Settis/6502/prog/SDcard/pulseView/goodRatio.png

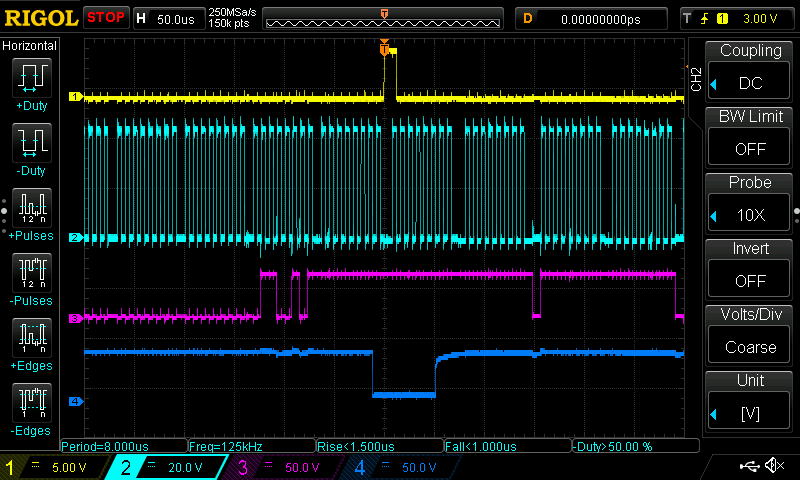
prog/SDcard/pulseView/goodRatio.png
