Settis/6502/prog/SDcard/pulseView/goodRatioZoom1.png

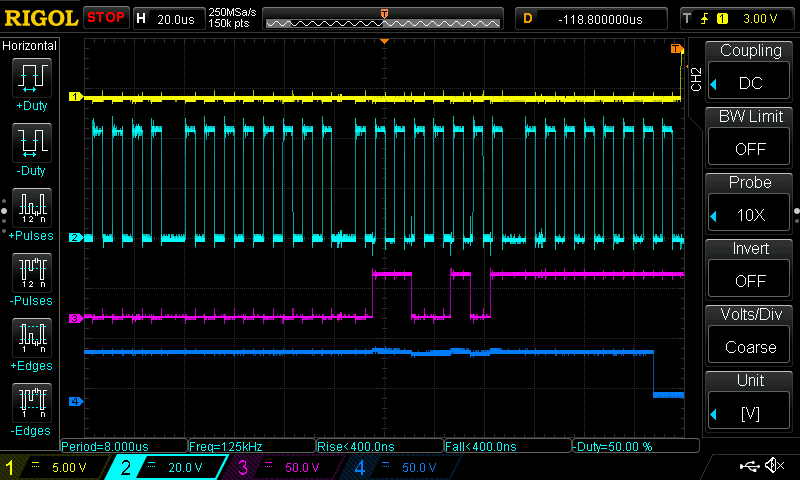
prog/SDcard/pulseView/goodRatioZoom1.png
