Settis/6502/prog/SDcard/pulseView/goodRatioZoom2.png

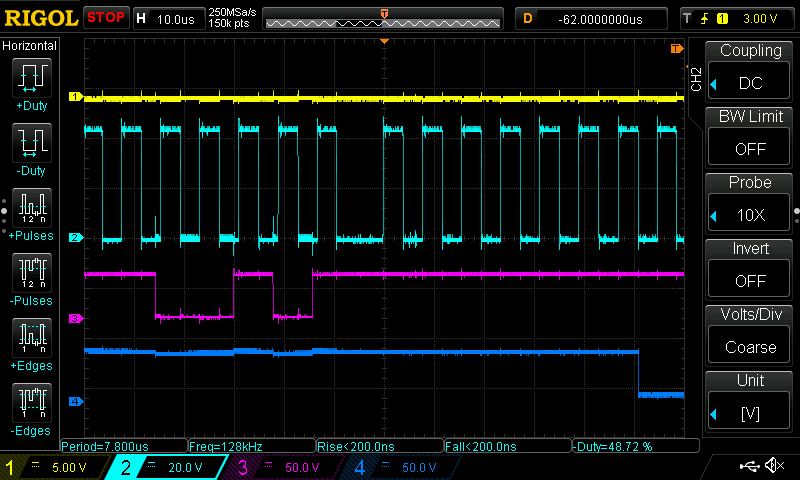
prog/SDcard/pulseView/goodRatioZoom2.png
