Settis/6502/prog/SDcard/pulseView/initial.png

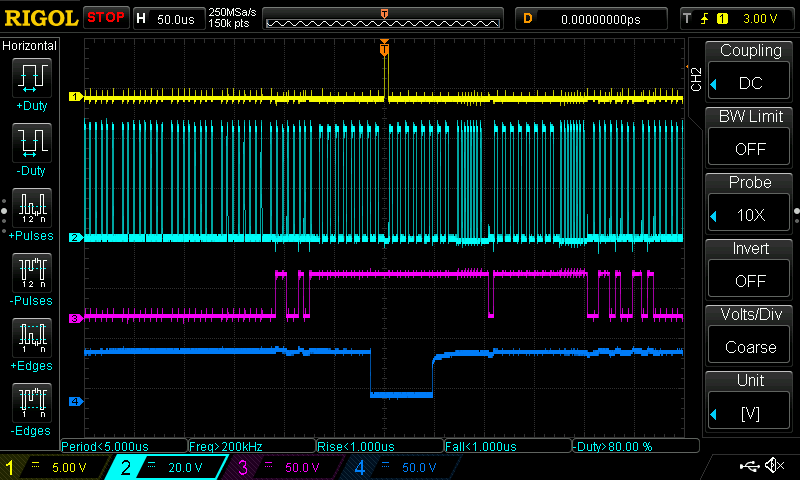
prog/SDcard/pulseView/initial.png
