Settis/6502/prog/SDcard/pulseView/initialZoom1.png

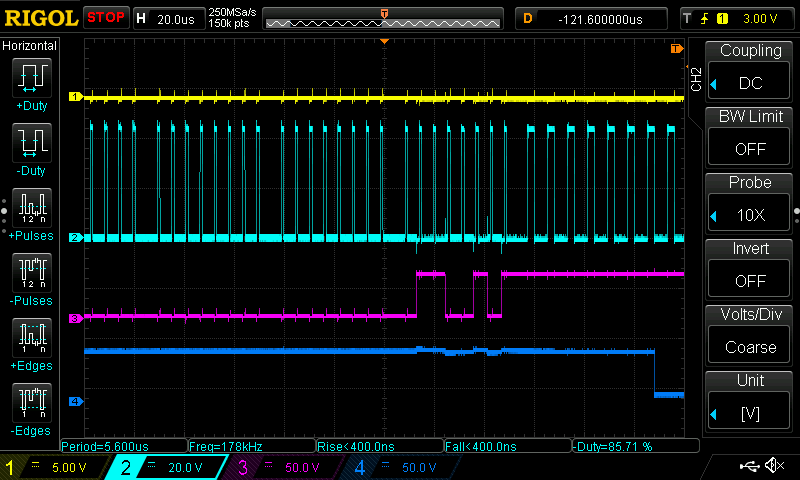
prog/SDcard/pulseView/initialZoom1.png
