Settis/6502/prog/SDcard/pulseView/initialZoom2.png

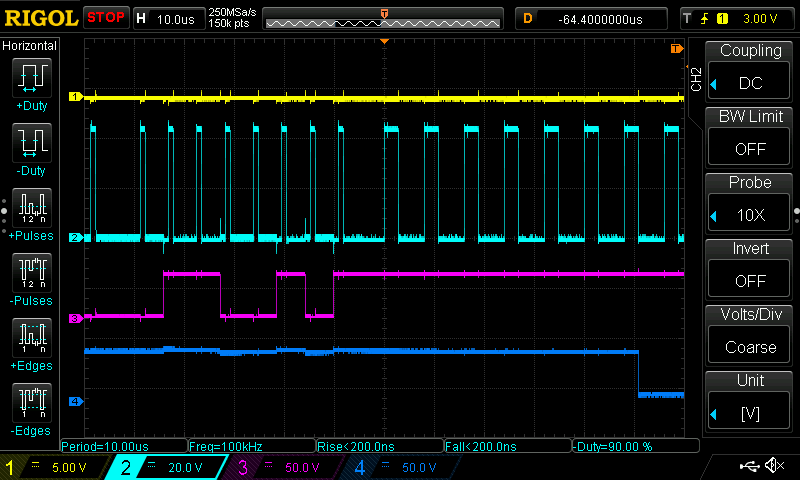
prog/SDcard/pulseView/initialZoom2.png
