Settis/6502/schematics/VGA_TO_VIA/VGA_TO_VIA.kicad_pcb

## KiCad design hardware/kicad/atmosmesh-bench/atmosmesh-bench.kicad_pcb

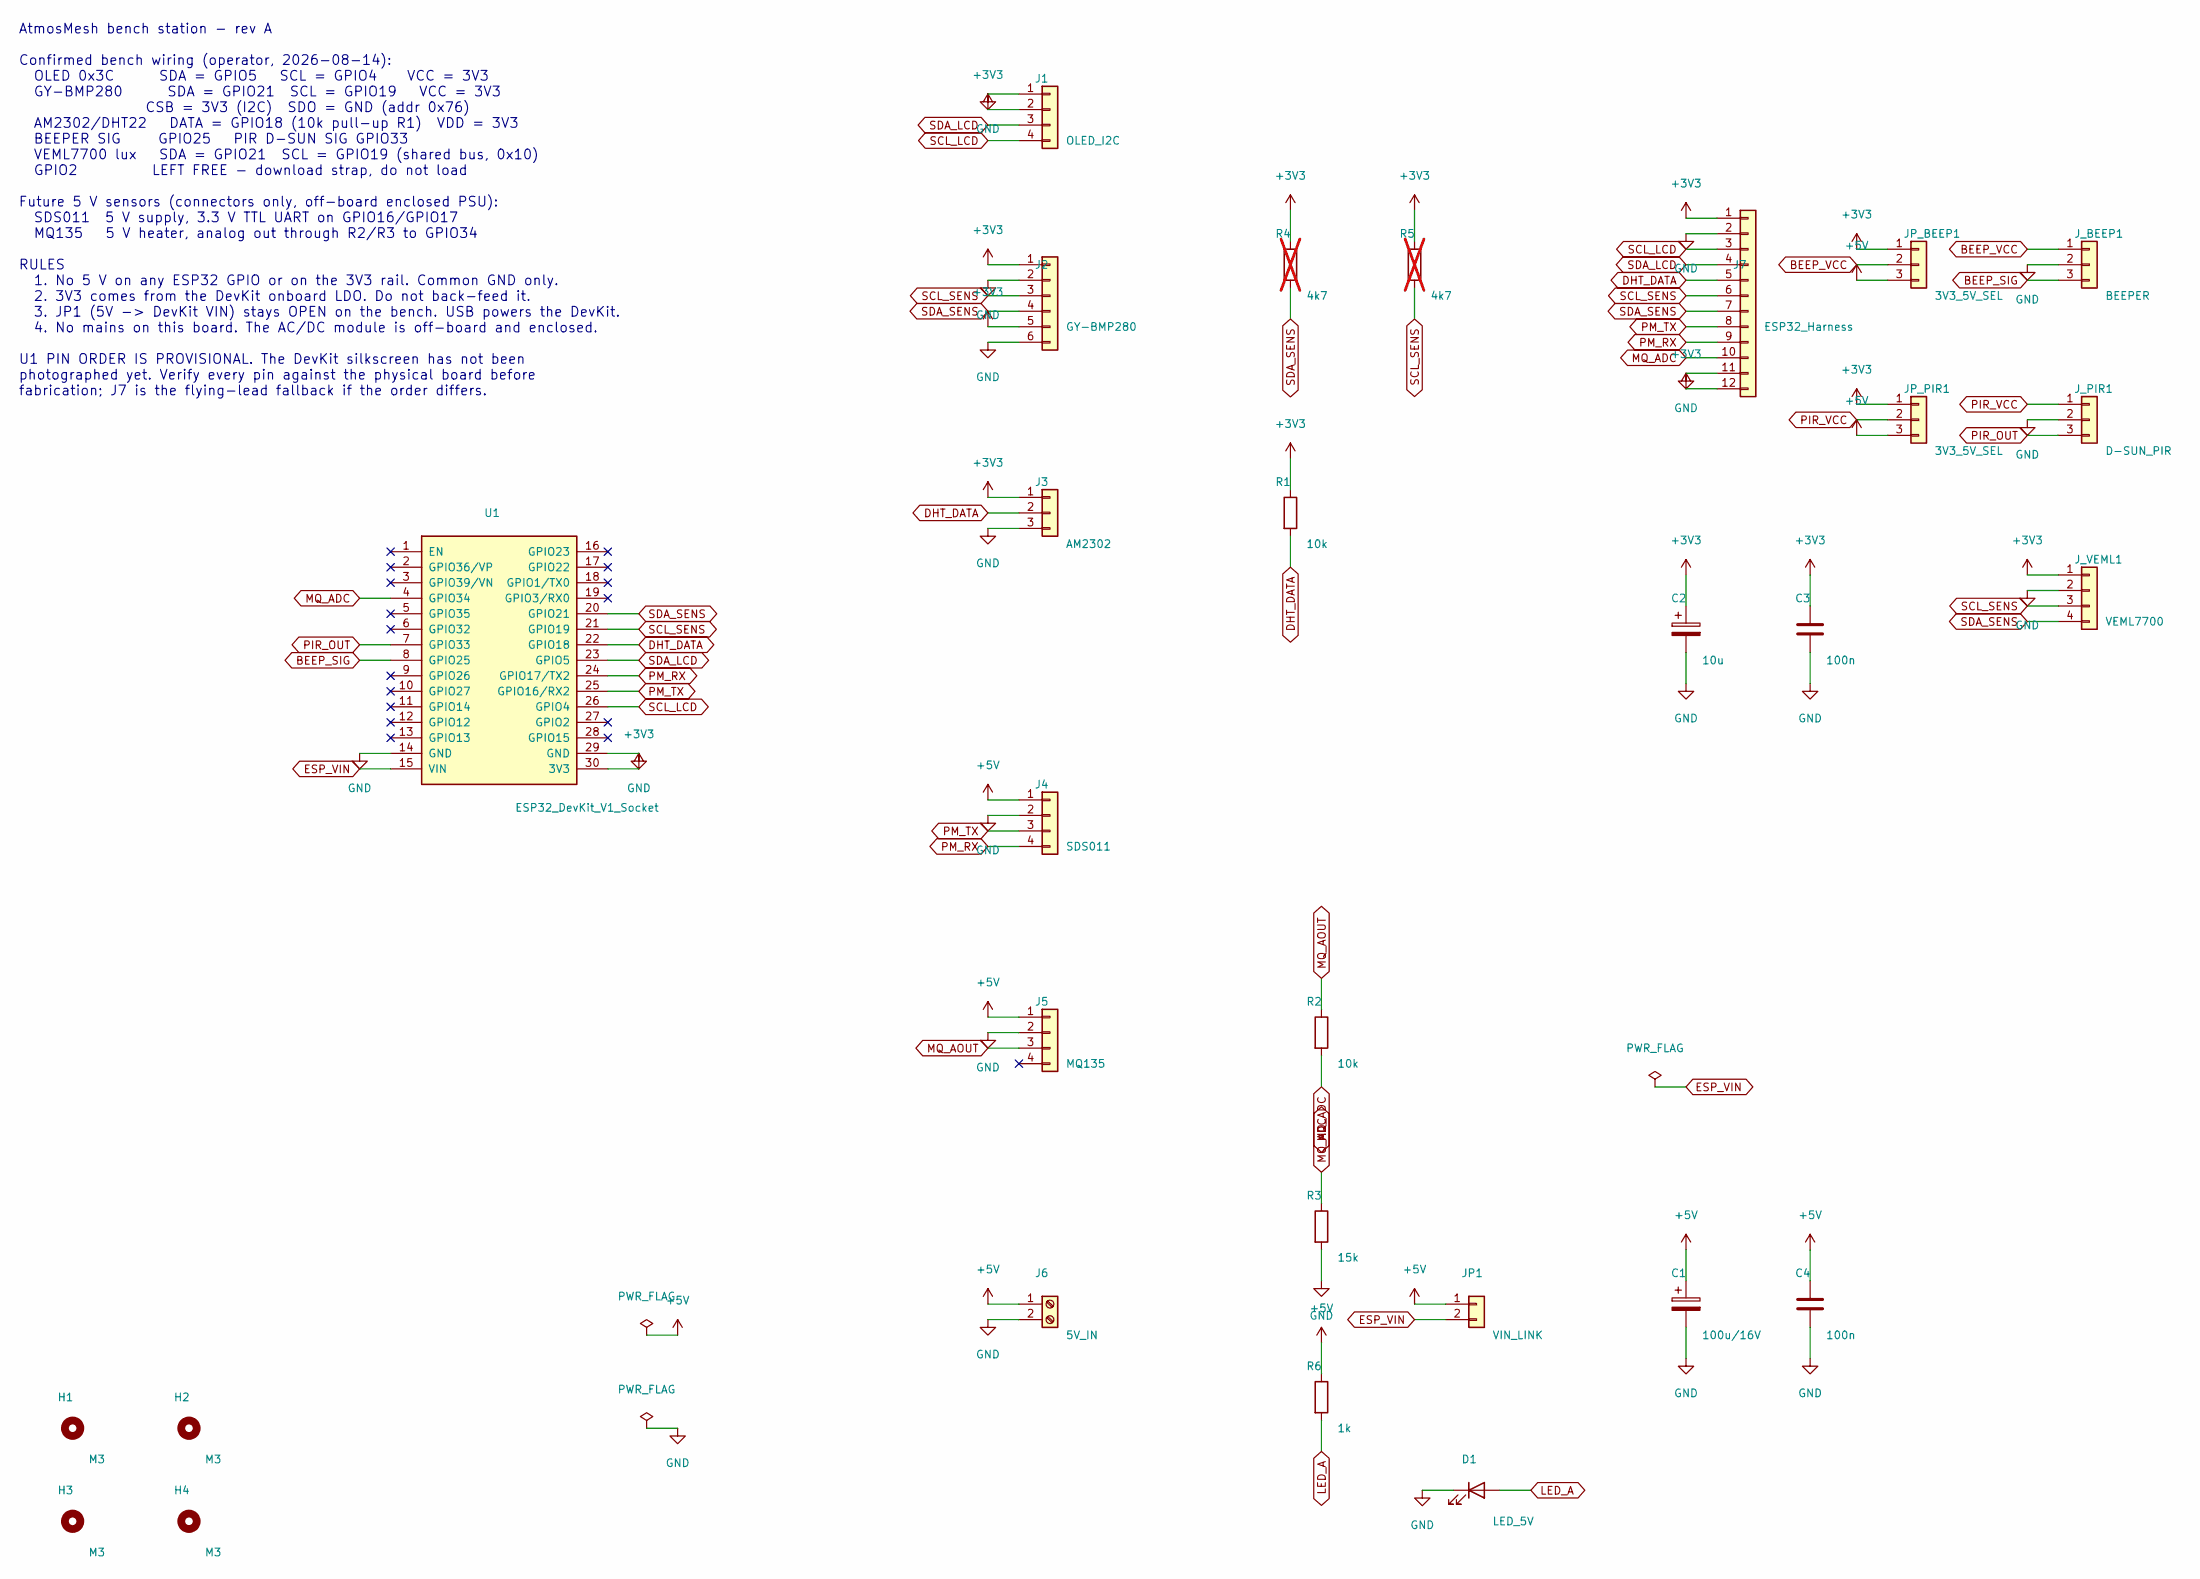
[picture p30: schematic atmosmesh-bench.kicad_sch, AtmosMesh bench station]

Parts:
C1: 100u/16V; CP_Radial_D6.3mm_P2.50mm
C2: 10u; CP_Radial_D5.0mm_P2.00mm
C3, C4: 100n; C_Disc_D5.0mm_W2.5mm_P5.00mm
D1: LED_5V; LED_D3.0mm
H1, H2, H3, H4: M3; MountingHole_3.2mm_M3
J1: OLED_I2C; PinHeader_1x04_P2.54mm_Vertical
J2: GY-BMP280; PinHeader_1x06_P2.54mm_Vertical
J3: AM2302; PinHeader_1x03_P2.54mm_Vertical
J4: SDS011; PinHeader_1x04_P2.54mm_Vertical
J5: MQ135; PinHeader_1x04_P2.54mm_Vertical
J6: 5V_IN; TerminalBlock_Phoenix_MKDS-1,5-2-5.08_1x02_P5.08mm_Horizont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
J7: ESP32_Harness; PinHeader_1x12_P2.54mm_Vertical
JP1: VIN_LINK; PinHeader_1x02_P2.54mm_Vertical
JP_BEEP1: 3V3_5V_SEL; PinHeader_1x03_P2.54mm_Vertical
JP_PIR1: 3V3_5V_SEL; PinHeader_1x03_P2.54mm_Vertical
J_BEEP1: BEEPER; PinHeader_1x03_P2.54mm_Vertical
J_PIR1: D-SUN_PIR; PinHeader_1x03_P2.54mm_Vertical
J_VEML1: VEML7700; PinHeader_1x04_P2.54mm_Vertical
R1, R2: 10k; R_Axial_DIN0207_L6.3mm_D2.5mm_P7.62mm_Horizontal
R3: 15k; R_Axial_DIN0207_L6.3mm_D2.5mm_P7.62mm_Horizontal
R4, R5: 4k7; R_Axial_DIN0207_L6.3mm_D2.5mm_P7.62mm_Horizontal; not fitted
R6: 1k; R_Axial_DIN0207_L6.3mm_D2.5mm_P7.62mm_Horizontal
U1: ESP32_DevKit_V1_Socket; ESP32_DevKit_1x15x2_P25.40mm

Connections:
+3V3: C2.1, C3.1, J1.2, J2.1, J2.5, J3.1, J7.1, J7.12, JP_BEEP1.1, JP_PIR1.1, J_VEML1.1, R1.1, R4.1, R5.1, U1.30 (3V3)
+5V: C1.1, C4.1, J4.1, J5.1, J6.1, JP1.1, JP_BEEP1.3, JP_PIR1.3, R6.1
BEEP_SIG: J_BEEP1.3, U1.8 (GPIO25)
BEEP_VCC: JP_BEEP1.2, J_BEEP1.1
DHT_DATA: J3.2, J7.5, R1.2, U1.22 (GPIO18)
ESP_VIN: JP1.2, U1.15 (VIN)
GND: C1.2, C2.2, C3.2, C4.2, D1.1 (K), J1.1, J2.2, J2.6, J3.3, J4.2, J5.2, J6.2, J7.2, J7.11, J_BEEP1.2, J_PIR1.2, J_VEML1.2, R3.2, U1.14 (GND), U1.29 (GND)
LED_A: D1.2 (A), R6.2
MQ_ADC: J7.10, R2.2, R3.1, U1.4 (GPIO34)
MQ_AOUT: J5.3, R2.1
PIR_OUT: J_PIR1.3, U1.7 (GPIO33)
PIR_VCC: JP_PIR1.2, J_PIR1.1
PM_RX: J4.4, J7.9, U1.24 (GPIO17/TX2)
PM_TX: J4.3, J7.8, U1.25 (GPIO16/RX2)
SCL_LCD: J1.4, J7.3, U1.26 (GPIO4)
SCL_SENS: J2.3, J7.6, J_VEML1.3, R5.2, U1.21 (GPIO19)
SDA_LCD: J1.3, J7.4, U1.23 (GPIO5)
SDA_SENS: J2.4, J7.7, J_VEML1.4, R4.2, U1.20 (GPIO21)

Notes on the sheet:
AtmosMesh bench station - rev A Confirmed bench wiring (operator, 2026-08-14): OLED 0x3C SDA = GPIO5 SCL = GPIO4 VCC = 3V3 GY-BMP280 SDA = GPIO21 SCL = GPIO19 VCC = 3V3 CSB = 3V3 (I2C) SDO = GND (addr 0x76) AM2302/DHT22 DATA = GPIO18 (10k pull-up R1) VDD = 3V3 BEEPER SIG GPIO25 PIR D-SUN SIG GPIO33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

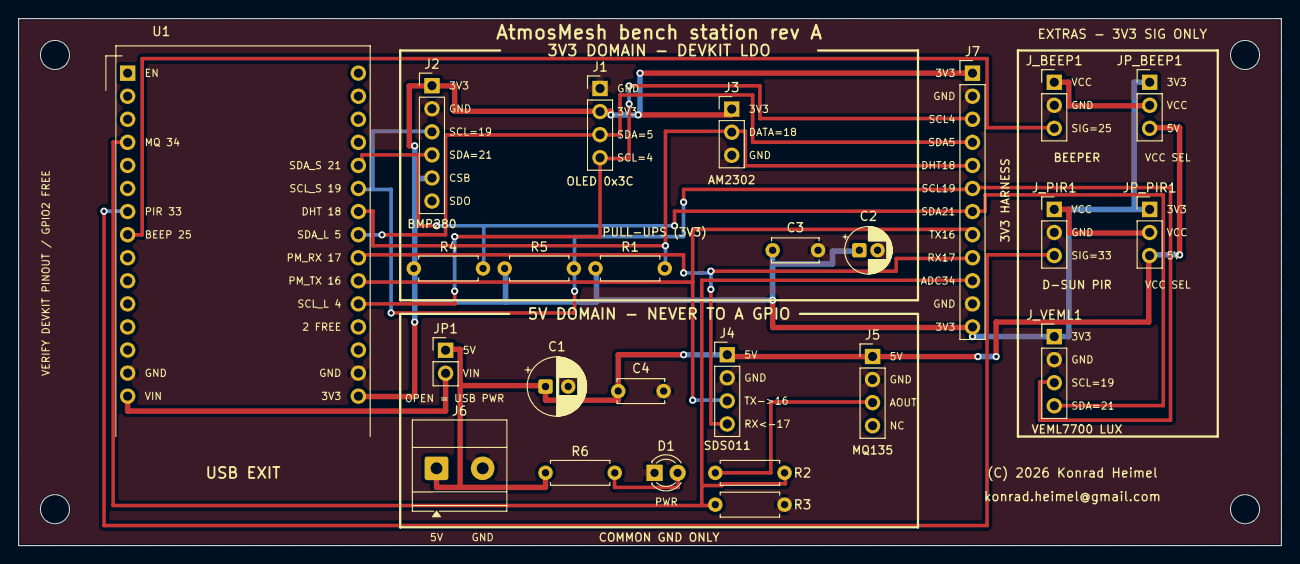
[picture p31: board atmosmesh-bench.kicad_pcb from above]

Board: 2 copper layers, 139.0 x 58.0 mm, 29 parts (0 on the bottom side), 18 nets.
