Settis/6502/logisim/progs/images.asm

satellite_data:
	dc $3d
	dc $66
	dc $4c
	dc $24
	dc $1b
	dc $1a
	dc $19
	dc $18
	dc $17
	dc $16
	dc $15
	dc $14
	dc $13
	dc $3c
	dc $3b
	dc $3a
	dc $34
	dc $33
	dc $32
	dc $5d
	dc $5c
	dc $52
	dc $51
	dc $50
	dc $4f
	dc $7e
	dc $7d
	dc $72
	dc $71
	dc $70
	dc $6f
	dc $6e
	dc $9f
	dc $9e
	dc $93
	dc $92
	dc $90
	dc $8f
	dc $8e
	dc $8d
	dc $bf
	dc $be
	dc $b4
	dc $b3
	dc $b0
	dc $af
	dc $ae
	dc $ad
	dc $ac
	dc $df
	dc $d5
	dc $d4
	dc $cf
	dc $ce
	dc $cd
	dc $cc
	dc $cb
	dc $ff
	dc $f6
	dc $f5
	dc $ef
	dc $ed
	dc $ec
	dc $eb
	dc $ea
	dc $1f
	dc $17
	dc $16
	dc $0f
	dc $0c
	dc $0b
	dc $0a
	dc $09
	dc $3f
	dc $38
	dc $37
	dc $36
	dc $35
	dc $30
	dc $2f
	dc $2b
	dc $2a
	dc $29
	dc $28
	dc $5f
	dc $59
	dc $58
	dc $56
	dc $55
	dc $54
	dc $51
	dc $50
	dc $4f
	dc $4a
	dc $49
	dc $48
	dc $47
	dc $7f
	dc $7e
	dc $7a
	dc $79
	dc $75
	dc $74
	dc $73
	dc $72
	dc $71
	dc $70
	dc $6f
	dc $69
	dc $68
	dc $67
	dc $66
	dc $9f
	dc $9e
	dc $9b
	dc $9a
	dc $94
	dc $93
	dc $92
	dc $91
	dc $90
	dc $8f
	dc $88
	dc $87
	dc $86
	dc $85
	dc $be
	dc $bd
	dc $bc
	dc $bb
	dc $b4
	dc $b3
	dc $b2
	dc $b1
	dc $b0
	dc $a7
	dc $a6
	dc $a5
	dc $a4
	dc $dd
	dc $dc
	dc $d5
	dc $d4
	dc $d3
	dc $d2
	dc $d1
	dc $d0
	dc $c6
	dc $c5
	dc $c4
	dc $c3
	dc $fd
	dc $fc
	dc $fb
	dc $fa
	dc $f6
	dc $f5
	dc $f4
	dc $f3
	dc $f2
	dc $f1
	dc $f0
	dc $ef
	dc $e5
	dc $e4
	dc $e3
	dc $e2
	dc $1d
	dc $1c
	dc $1b
	dc $1a
	dc $19
	dc $18
	dc $17
	dc $16
	dc $15
	dc $14
	dc $13
	dc $10
	dc $0f
	dc $0e
	dc $04
	dc $03
	dc $02
	dc $01
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
	dc.w artichoke_data
	dc.w dill_data
	dc.w blueberries_data
	dc.w satellite2_data
	dc.w satellite3_data
	dc.w cherry_data
	dc.w atoms_data
	dc.w chiliPepper_data
	dc.w onion_data
	dc.w rocket_data
	dc.w microchip_data
	dc.w robot_data
	dc.w robot2_data
	dc.w garlic_data
	dc.w floppy_data
	dc.w broccoli_data
