Settis/6502/prog/std/initSegments.asm

    IFNCONST ZP_VARS_START
ZP_VARS_START = $0
    ENDIF
    
    SEG.U zpVars
    ORG ZP_VARS_START

    IFNCONST CODE_START
CODE_START = $200
    ENDIF

    SEG code
    ORG CODE_START

    IFNCONST UPPER_RAM_START
UPPER_RAM_START = $7FFF
    ENDIF

    SEG.U upperRam
    ORG UPPER_RAM_START
