Settis/6502/prog/std/io_errors.asm

IO_OK = $0
IO_END_OF_FILE = $1
IO_FILE_NOT_FOUND = $2
IO_INVALID_FILENAME_FORMAT = $3
IO_SD_BUSY_BEFORE_GO_IDLE_STATE = $4
IO_SD_BUSY_AFTER_GO_IDLE_STATE = $5
IO_SD_NOT_IDLE_AFTER_GO_IDLE_STATE = $6
IO_SD_BUSY_BEFORE_SEND_IF_COND = $7
IO_SD_BUSY_AFTER_SEND_IF_COND = $8
IO_SD_NOT_IDLE_AFTER_SEND_IF_COND = $9
IO_SD_BUSY_BEFORE_APP_CMD = $A
IO_SD_BUSY_AFTER_APP_CMD = $B
IO_SD_BUSY_BEFORE_APP_SEND_OP_COND = $C
IO_SD_BUSY_AFTER_APP_SEND_OP_COND = $D
IO_SD_ERROR_AFTER_APP_SEND_OP_COND = $E
IO_SD_BUSY_BEFORE_READ_SECTOR = $F
IO_SD_BUSY_AFTER_READ_SECTOR = $10
IO_SD_ERROR_AFTER_READ_SECTOR = $11
IO_SD_DATA_TOKEN_DID_NOT_RECEIVED_AFTER_READ_SECTOR = $12
IO_WRONG_BOOT_SIGNATURE = $13
IO_WRONG_PARTITION_TYPE = $14
IO_WRONG_BYTES_PER_LOGICAL_SECTOR = $15
IO_WRONG_FATS_NUMBER = $16
IO_WRONG_FAT_MEDIA_DESCRIPTOR = $17
IO_ZERO_SECTORS_PER_CLUSTER = $18
IO_FAT_END_OF_CLUSTERS = $19
