Settis/6502/logisim/tools/microcodeSpec.yaml

address:
  - type: counter
    size: 4
  - type: instruction
    size: 8
  - type: condition
    name: CF
  - type: condition
    name: ZF
  - type: condition
    name: VF
  - type: condition
    name: NF
outBits:
  - name: AddrSelecter
    type: enum
    offset: 0
    values:
      - PC
      - Addr
      - ZP
      - SP
  - name: CntLIn
    offset: 2
  - name: CntHIn
    offset: 3
  - name: CntEn
    offset: 4
  - name: InstIn
    offset: 5
  - name: AluM
    offset: 6
  - name: SecondSelect
    type: enum
    offset: 7
    values:
      - Alu0
      - AluA
      - AluX
      - AluY
      - AluSp
      - AluAddrL
      - AluAddrH
      - AluB
  - name: OpSelect
    type: enum
    offset: 10
    values:
      - Add
      - Sub
      - Or
      - And
      - Xor
      - ASL
      - LSR
      - RTL
      - RTR
      - AddAddrLAndY
  - name: AluOutSelect
    type: enum
    offset: 14
    values:
      - AluToB
      - AluToA
      - AluToX
      - AluToY
      - AluToSp
      - AluToAddrH
      - AluToAddrL
      - AluToF
  - name: DataOutSelect
    type: enum
    offset: 17
    values:
      - DataOutNull
      - DataOutA
      - DataOutB
      - DataOutPcH
      - DataOutPcL
      - DataOutX
      - DataOutY
      - DataOutF
  - name: FlagInst
    type: enum
    offset: 20
    values:
      - FlagNone
      - ClearCarry
      - SetCarry
      - ClearInt
      - SetInt
      - ClearOverfl
      - ClearDec
      - SetDec
  - name: UseCF
    type: enum
    offset: 23
    values:
      - CF0
      - CF1
      - LCF
      - CF
  - name: CFEn
    offset: 25
  - name: ZFEn
    offset: 26
  - name: VFEn
    offset: 27
  - name: NFEn
    offset: 28
  - name: AddrShift
    offset: 29
  - name: MicRst
    offset: 30
defaultStartSteps:
  - InstIn | CntEn
defaultEndSteps:
  - MicRst
prefixSteps:
  - name: ZP
    steps:
      - AluToAddrH
      - AluM | AluToAddrL | CntEn
  - name: ZPX
    steps:
      - AluToAddrH
      - AluM | AluX | Add | AluToAddrL | CntEn
  - name: ZPY
    steps:
      - AluToAddrH
      - AluM | AluY | Add | AluToAddrL | CntEn
  - name: Abs
    steps:
      - AluM | AluToAddrL | CntEn
      - AluM | AluToAddrH | CntEn
  - name: AbsX
    steps:
      - AluM | AluX | Add | AluToAddrL | CntEn
      - AluM | LCF | Add | AluToAddrH | CntEn
  - name: AbsY
    steps:
      - AluM | AluY | Add | AluToAddrL | CntEn
      - AluM | LCF | Add | AluToAddrH | CntEn
  - name: IndX
    steps:
      - AluToAddrH
      - AluM | AluX | Add | AluToAddrL | CntEn
      - Addr | AluM | AluToB
      - AluAddrL | CF1 | Add | AluToAddrL
      - Addr | AluM | AluToAddrH
      - AluB | AluToAddrL
  - name: IndY
    steps:
      - AluToAddrH
      - AluM | AluToAddrL | CntEn
      - Addr | AluM | AluToB
      - AluAddrL | CF1 | Add | AluToAddrL
      - Addr | AluM | AluToAddrH
      - AluB | AluToAddrL
      - AddAddrLAndY | AluToAddrL
      - AluAddrH | LCF | Add | AluToAddrH
  - name: BrPos
    steps:
      - AluM | AluToB | CntEn
      - AluB | AddrShift | CntLIn | CntHIn
  - name: BrNeg
    steps:
      - CntEn
commands:
  - name: "ADC #$44"
    value: 0x69
    steps:
      - AluM | AluA | Add | CF | AluToA | CntEn | NFEn | VFEn | ZFEn | CFEn
  - name: "ADC $44"
    value: 0x65
    prefix: ZP
    steps:
      - Addr | AluM | AluA | Add | CF | AluToA | NFEn | VFEn | ZFEn | CFEn
  - name: "ADC $44,X"
    value: 0x75
    prefix: ZPX
    steps:
      - Addr | AluM | AluA | Add | CF | AluToA | NFEn | VFEn | ZFEn | CFEn
  - name: "ADC $4400"
    value: 0x6d
    prefix: Abs
    steps:
      - Addr | AluM | AluA | Add | CF | AluToA | NFEn | VFEn | ZFEn | CFEn
  - name: "ADC $4400,X"
    value: 0x7d
    prefix: AbsX
    steps:
      - Addr | AluM | AluA | Add | CF | AluToA | NFEn | VFEn | ZFEn | CFEn
  - name: "ADC $4400,Y"
    value: 0x79
    prefix: AbsY
    steps:
      - Addr | AluM | AluA | Add | CF | AluToA | NFEn | VFEn | ZFEn | CFEn
  - name: "ADC ($44,X)"
    value: 0x61
    prefix: IndX
    steps:
      - Addr | AluM | AluA | Add | CF | AluToA | NFEn | VFEn | ZFEn | CFEn
  - name: "ADC ($44),Y"
    value: 0x71
    prefix: IndY
    steps:
      - Addr | AluM | AluA | Add | CF | AluToA | NFEn | VFEn | ZFEn | CFEn
  - name: "AND #$44"
    value: 0x29
    steps:
      - AluM | AluA | And | AluToA | NFEn | ZFEn | CntEn
  - name: "AND $44"
    value: 0x25
    prefix: ZP
    steps:
      - Addr | AluM | AluA | And | AluToA | NFEn | ZFEn
  - name: "AND $44,X"
    value: 0x35
    prefix: ZPX
    steps:
      - Addr | AluM | AluA | And | AluToA | NFEn | ZFEn
  - name: "AND $4400"
    value: 0x2d
    prefix: Abs
    steps:
      - Addr | AluM | AluA | And | AluToA | NFEn | ZFEn
  - name: "AND $4400,X"
    value: 0x3d
    prefix: AbsX
    steps:
      - Addr | AluM | AluA | And | AluToA | NFEn | ZFEn
  - name: "AND $4400,Y"
    value: 0x39
    prefix: AbsY
    steps:
      - Addr | AluM | AluA | And | AluToA | NFEn | ZFEn
  - name: "AND ($44,X)"
    value: 0x21
    prefix: IndX
    steps:
      - Addr | AluM | AluA | And | AluToA | NFEn | ZFEn
  - name: "AND ($44),Y"
    value: 0x31
    prefix: IndY
    steps:
      - Addr | AluM | AluA | And | AluToA | NFEn | ZFEn
  - name: "ASL A"
    value: 0x0a
    steps:
      - ASL | AluToA | NFEn | ZFEn | CFEn
  - name: "ASL $44"
    value: 0x06
    prefix: ZP
    steps:
      - Addr | AluM | ASL | AluToB | NFEn | ZFEn | CFEn
      - Addr | DataOutB
  - name: "ASL $44,X"
    value: 0x16
    prefix: ZPX
    steps:
      - Addr | AluM | ASL | AluToB | NFEn | ZFEn | CFEn
      - Addr | DataOutB
  - name: "ASL $4400"
    value: 0x0e
    prefix: Abs
    steps:
      - Addr | AluM | ASL | AluToB | NFEn | ZFEn | CFEn
      - Addr | DataOutB
  - name: "ASL $4400,X"
    value: 0x1e
    prefix: AbsX
    steps:
      - Addr | AluM | ASL | AluToB | NFEn | ZFEn | CFEn
      - Addr | DataOutB
  - name: "BIT $44" # Sets only Z bit
    value: 0x24
    prefix: ZP
    steps:
      - Addr | AluM | AluA | And | ZFEn
  - name: "BIT $4400" # Sets only Z bit
    value: 0x2c
    prefix: Abs
    steps:
      - Addr | AluM | AluA | And | ZFEn
  - name: "BPL+"
    value: 0x10
    condition:
      - NF_0
    prefix: BrPos
    steps: []
  - name: "BPL-"
    value: 0x10
    condition:
      - NF_1
    prefix: BrNeg
    steps: []
  - name: "BMI+"
    value: 0x30
    condition:
      - NF_1
    prefix: BrPos
    steps: []
  - name: "BMI-"
    value: 0x30
    condition:
      - NF_0
    prefix: BrNeg
    steps: []
  - name: "BVC+"
    value: 0x50
    condition:
      - VF_0
    prefix: BrPos
    steps: []
  - name: "BVC-"
    value: 0x50
    condition:
      - VF_1
    prefix: BrNeg
    steps: []
  - name: "BVS+"
    value: 0x70
    condition:
      - VF_1
    prefix: BrPos
    steps: []
  - name: "BVS-"
    value: 0x70
    condition:
      - VF_0
    prefix: BrNeg
    steps: []
  - name: "BCC+"
    value: 0x90
    condition:
      - CF_0
    prefix: BrPos
    steps: []
  - name: "BCC-"
    value: 0x90
    condition:
      - CF_1
    prefix: BrNeg
    steps: []
  - name: "BCS+"
    value: 0xb0
    condition:
      - CF_1
    prefix: BrPos
    steps: []
  - name: "BCS-"
    value: 0xb0
    condition:
      - CF_0
    prefix: BrNeg
    steps: []
  - name: "BNE+"
    value: 0xd0
    condition:
      - ZF_0
    prefix: BrPos
    steps: []
  - name: "BNE-"
    value: 0xd0
    condition:
      - ZF_1
    prefix: BrNeg
    steps: []
  - name: "BEQ+"
    value: 0xf0
    condition:
      - ZF_1
    prefix: BrPos
    steps: []
  - name: "BEQ-"
    value: 0xf0
    condition:
      - ZF_0
    prefix: BrNeg
    steps: []
  # BRK not implemented
  - name: "CMP #$44"
    value: 0xc9
    steps:
      - AluM | AluA | Sub | NFEn | ZFEn | CFEn | CntEn
  - name: "CMP $44"
    value: 0xc5
    prefix: ZP
    steps:
      - Addr | AluM | AluA | Sub | NFEn | ZFEn | CFEn
  - name: "CMP $44,X"
    value: 0xd5
    prefix: ZPX
    steps:
      - Addr | AluM | AluA | Sub | NFEn | ZFEn | CFEn
  - name: "CMP $4400"
    value: 0xcd
    prefix: Abs
    steps:
      - Addr | AluM | AluA | Sub | NFEn | ZFEn | CFEn
  - name: "CMP $4400,X"
    value: 0xdd
    prefix: AbsX
    steps:
      - Addr | AluM | AluA | Sub | NFEn | ZFEn | CFEn
  - name: "CMP $4400,Y"
    value: 0xd9
    prefix: AbsY
    steps:
      - Addr | AluM | AluA | Sub | NFEn | ZFEn | CFEn
  - name: "CMP ($44,X)"
    value: 0xc1
    prefix: IndX
    steps:
      - Addr | AluM | AluA | Sub | NFEn | ZFEn | CFEn
  - name: "CMP ($44),Y"
    value: 0xd1
    prefix: IndY
    steps:
      - Addr | AluM | AluA | Sub | NFEn | ZFEn | CFEn
  - name: "CPX #$44"
    value: 0xe0
    steps:
      - AluM | AluX | Sub | NFEn | ZFEn | CFEn | CntEn
  - name: "CPX $44"
    value: 0xe4
    prefix: ZP
    steps:
      - Addr | AluM | AluX | Sub | NFEn | ZFEn | CFEn
  - name: "CPX $4400"
    value: 0xec
    prefix: Abs
    steps:
      - Addr | AluM | AluX | Sub | NFEn | ZFEn | CFEn
  - name: "CPY #$44"
    value: 0xc0
    steps:
      - AluM | AluY | Sub | NFEn | ZFEn | CFEn | CntEn
  - name: "CPY $44"
    value: 0xc4
    prefix: ZP
    steps:
      - Addr | AluM | AluY | Sub | NFEn | ZFEn | CFEn
  - name: "CPY $4400"
    value: 0xcc
    prefix: Abs
    steps:
      - Addr | AluM | AluY | Sub | NFEn | ZFEn | CFEn
  - name: "DEC $44"
    value: 0xc6
    prefix: ZP
    steps:
      - Addr | AluM | AluToB
      - AluB | Sub | CF1 | AluToB | NFEn | ZFEn
      - Addr | DataOutB
  - name: "DEC $44,X"
    value: 0xd6
    prefix: ZPX
    steps:
      - Addr | AluM | AluToB
      - AluB | Sub | CF1 | AluToB | NFEn | ZFEn
      - Addr | DataOutB
  - name: "DEC $4400"
    value: 0xce
    prefix: Abs
    steps:
      - Addr | AluM | AluToB
      - AluB | Sub | CF1 | AluToB | NFEn | ZFEn
      - Addr | DataOutB
  - name: "DEC $4400,X"
    value: 0xde
    prefix: AbsX
    steps:
      - Addr | AluM | AluToB
      - AluB | Sub | CF1 | AluToB | NFEn | ZFEn
      - Addr | DataOutB
  - name: "EOR #$44"
    value: 0x49
    steps:
      - AluM | AluA | Xor | AluToA | NFEn | ZFEn | CntEn
  - name: "EOR $44"
    value: 0x45
    prefix: ZP
    steps:
      - Addr | AluM | AluA | Xor | AluToA | NFEn | ZFEn
  - name: "EOR $44,X"
    value: 0x55
    prefix: ZPX
    steps:
      - Addr | AluM | AluA | Xor | AluToA | NFEn | ZFEn
  - name: "EOR $4400"
    value: 0x4d
    prefix: Abs
    steps:
      - Addr | AluM | AluA | Xor | AluToA | NFEn | ZFEn
  - name: "EOR $4400,X"
    value: 0x5d
    prefix: AbsX
    steps:
      - Addr | AluM | AluA | Xor | AluToA | NFEn | ZFEn
  - name: "EOR $4400,Y"
    value: 0x59
    prefix: AbsY
    steps:
      - Addr | AluM | AluA | Xor | AluToA | NFEn | ZFEn
  - name: "EOR ($44,X)"
    value: 0x41
    prefix: IndX
    steps:
      - Addr | AluM | AluA | Xor | AluToA | NFEn | ZFEn
  - name: "EOR ($44),Y"
    value: 0x51
    prefix: IndY
    steps:
      - Addr | AluM | AluA | Xor | AluToA | NFEn | ZFEn
  - name: "CLC"
    value: 0x18
    steps:
      - ClearCarry
  - name: "SEC"
    value: 0x38
    steps:
      - SetCarry
  - name: "CLI"
    value: 0x58
    steps:
      - ClearInt
  - name: "SEI"
    value: 0x78
    steps:
      - SetInt
  - name: "CLV"
    value: 0xb8
    steps:
      - ClearOverfl
  - name: "CLD"
    value: 0xd8
    steps:
      - ClearDec
  - name: "SED"
    value: 0xf8
    steps:
      - SetDec
  - name: "INC $44"
    value: 0xe6
    prefix: ZP
    steps:
      - Addr | AluM | Add | CF1 | AluToB | NFEn | ZFEn
      - Addr | DataOutB
  - name: "INC $44,X"
    value: 0xf6
    prefix: ZPX
    steps:
      - Addr | AluM | Add | CF1 | AluToB | NFEn | ZFEn
      - Addr | DataOutB
  - name: "INC $4400"
    value: 0xee
    prefix: Abs
    steps:
      - Addr | AluM | Add | CF1 | AluToB | NFEn | ZFEn
      - Addr | DataOutB
  - name: "INC $4400,X"
    value: 0xfe
    prefix: AbsX
    steps:
      - Addr | AluM | Add | CF1 | AluToB | NFEn | ZFEn
      - Addr | DataOutB
  - name: "JMP $5597"
    value: 0x4c
    prefix: Abs
    steps:
      - CntLIn | CntHIn
  - name: "JMP ($5597)"
    value: 0x6c
    prefix: Abs
    steps:
      - Addr | AluM | AluToB
      - AluAddrL | CF1 | Add | AluToAddrL
      - AluAddrH | LCF | Add | AluToAddrH
      - Addr | AluM | AluToAddrH
      - AluB | AluToAddrL
      - CntLIn | CntHIn
  - name: "JSR"
    value: 0x20
    steps:
      - AluM | AluToAddrL | CntEn
      - AluM | AluToAddrH
      - SP | DataOutPcH
      - AluSp | Sub | CF1 | AluToSp
      - SP | DataOutPcL
      - AluSp | Sub | CF1 | AluToSp
      - CntLIn | CntHIn
  - name: "LDA #$44"
    value: 0xA9
    steps:
      - AluM | AluToA | NFEn | ZFEn | CntEn
  - name: "LDA $44"
    value: 0xA5
    prefix: ZP
    steps:
      - Addr | AluM | AluToA | NFEn | ZFEn
  - name: "LDA $44,X"
    value: 0xB5
    prefix: ZPX
    steps:
      - Addr | AluM | AluToA | NFEn | ZFEn
  - name: "LDA $4400"
    value: 0xAD
    prefix: Abs
    steps:
      - Addr | AluM | AluToA | NFEn | ZFEn
  - name: "LDA $4400,X"
    value: 0xBD
    prefix: AbsX
    steps:
      - Addr | AluM | AluToA | NFEn | ZFEn
  - name: "LDA $4400,Y"
    value: 0xB9
    prefix: AbsY
    steps:
      - Addr | AluM | AluToA | NFEn | ZFEn
  - name: "LDA ($44,X)"
    value: 0xA1
    prefix: IndX
    steps:
      - Addr | AluM | AluToA | NFEn | ZFEn
  - name: "LDA ($44),Y"
    value: 0xB1
    prefix: IndY
    steps:
      - Addr | AluM | AluToA | NFEn | ZFEn
  - name: "LDX #$44"
    value: 0xA2
    steps:
      - AluM | AluToX | NFEn | ZFEn | CntEn
  - name: "LDX $44"
    value: 0xA6
    prefix: ZP
    steps:
      - Addr | AluM | AluToX | NFEn | ZFEn
  - name: "LDX $44,Y"
    value: 0xb6
    prefix: ZPY
    steps:
      - Addr | AluM | AluToX | NFEn | ZFEn
  - name: "LDX $4400"
    value: 0xAe
    prefix: Abs
    steps:
      - Addr | AluM | AluToX | NFEn | ZFEn
  - name: "LDX $4400,Y"
    value: 0xbe
    prefix: AbsY
    steps:
      - Addr | AluM | AluToX | NFEn | ZFEn
  - name: "LDY #$44"
    value: 0xA0
    steps:
      - AluM | AluToY | NFEn | ZFEn | CntEn
  - name: "LDY $44"
    value: 0xA4
    prefix: ZP
    steps:
      - Addr | AluM | AluToY | NFEn | ZFEn
  - name: "LDY $44,X"
    value: 0xb4
    prefix: ZPX
    steps:
      - Addr | AluM | AluToY | NFEn | ZFEn
  - name: "LDY $4400"
    value: 0xAc
    prefix: Abs
    steps:
      - Addr | AluM | AluToY | NFEn | ZFEn
  - name: "LDY $4400,X"
    value: 0xbc
    prefix: AbsX
    steps:
      - Addr | AluM | AluToY | NFEn | ZFEn
  - name: "LSR A"
    value: 0x4a
    steps:
      - LSR | AluToA | NFEn | ZFEn | CFEn
  - name: "LSR $44"
    value: 0x46
    prefix: ZP
    steps:
      - Addr | AluM | LSR | AluToB | NFEn | ZFEn | CFEn
      - Addr | DataOutB
  - name: "LSR $44,X"
    value: 0x56
    prefix: ZPX
    steps:
      - Addr | AluM | LSR | AluToB | NFEn | ZFEn | CFEn
      - Addr | DataOutB
  - name: "LSR $4400"
    value: 0x4e
    prefix: Abs
    steps:
      - Addr | AluM | LSR | AluToB | NFEn | ZFEn | CFEn
      - Addr | DataOutB
  - name: "LSR $4400,X"
    value: 0x5e
    prefix: AbsX
    steps:
      - Addr | AluM | LSR | AluToB | NFEn | ZFEn | CFEn
      - Addr | DataOutB
  - name: "NOP"
    value: 0xea
    steps:
      - AluM
  - name: "ORA #$44"
    value: 0x09
    steps:
      - AluM | AluA | Or | AluToA | NFEn | ZFEn | CntEn
  - name: "ORA $44"
    value: 0x05
    prefix: ZP
    steps:
      - Addr | AluM | AluA | Or | AluToA | NFEn | ZFEn
  - name: "ORA $44,X"
    value: 0x15
    prefix: ZPX
    steps:
      - Addr | AluM | AluA | Or | AluToA | NFEn | ZFEn
  - name: "ORA $4400"
    value: 0x0d
    prefix: Abs
    steps:
      - Addr | AluM | AluA | Or | AluToA | NFEn | ZFEn
  - name: "ORA $4400,X"
    value: 0x1d
    prefix: AbsX
    steps:
      - Addr | AluM | AluA | Or | AluToA | NFEn | ZFEn
  - name: "ORA $4400,Y"
    value: 0x19
    prefix: AbsY
    steps:
      - Addr | AluM | AluA | Or | AluToA | NFEn | ZFEn
  - name: "ORA ($44,X)"
    value: 0x01
    prefix: IndX
    steps:
      - Addr | AluM | AluA | Or | AluToA | NFEn | ZFEn
  - name: "ORA ($44),Y"
    value: 0x11
    prefix: IndY
    steps:
      - Addr | AluM | AluA | Or | AluToA | NFEn | ZFEn
  - name: "TAX"
    value: 0xAA
    steps:
      - AluA | AluToX | NFEn | ZFEn
  - name: "TXA"
    value: 0x8a
    steps:
      - AluX | AluToA | NFEn | ZFEn
  - name: "DEX"
    value: 0xca
    steps:
      - AluX | Sub | CF1 | AluToX | NFEn | ZFEn
  - name: "INX"
    value: 0xe8
    steps:
      - AluX | Add | CF1 | AluToX | NFEn | ZFEn
  - name: "TAY"
    value: 0xa8
    steps:
      - AluA | AluToY | NFEn | ZFEn
  - name: "TYA"
    value: 0x98
    steps:
      - AluY | AluToA | NFEn | ZFEn
  - name: "DEY"
    value: 0x88
    steps:
      - AluY | Sub | CF1 | AluToY | NFEn | ZFEn
  - name: "INY"
    value: 0xc8
    steps:
      - AluY | Add | CF1 | AluToY | NFEn | ZFEn
  - name: "ROL A"
    value: 0x2a
    steps:
      - RTL | CF | AluToA | NFEn | ZFEn | CFEn
  - name: "ROL $44"
    value: 0x26
    prefix: ZP
    steps:
      - Addr | AluM | RTL | CF | AluToB | NFEn | ZFEn | CFEn
      - Addr | DataOutB
  - name: "ROL $44,X"
    value: 0x36
    prefix: ZPX
    steps:
      - Addr | AluM | RTL | CF | AluToB | NFEn | ZFEn | CFEn
      - Addr | DataOutB
  - name: "ROL $4400"
    value: 0x2e
    prefix: Abs
    steps:
      - Addr | AluM | RTL | CF | AluToB | NFEn | ZFEn | CFEn
      - Addr | DataOutB
  - name: "ROL $4400,X"
    value: 0x3e
    prefix: AbsX
    steps:
      - Addr | AluM | RTL | CF | AluToB | NFEn | ZFEn | CFEn
      - Addr | DataOutB
  - name: "ROR A"
    value: 0x6a
    steps:
      - RTR | CF | AluToA | NFEn | ZFEn | CFEn
  - name: "ROR $44"
    value: 0x66
    prefix: ZP
    steps:
      - Addr | AluM | RTR | CF | AluToB | NFEn | ZFEn | CFEn
      - Addr | DataOutB
  - name: "ROR $44,X"
    value: 0x76
    prefix: ZPX
    steps:
      - Addr | AluM | RTR | CF | AluToB | NFEn | ZFEn | CFEn
      - Addr | DataOutB
  - name: "ROR $4400"
    value: 0x6e
    prefix: Abs
    steps:
      - Addr | AluM | RTR | CF | AluToB | NFEn | ZFEn | CFEn
      - Addr | DataOutB
  - name: "ROR $4400,X"
    value: 0x7e
    prefix: AbsX
    steps:
      - Addr | AluM | RTR | CF | AluToB | NFEn | ZFEn | CFEn
      - Addr | DataOutB
  # RTI is not implemented
  - name: "RTS"
    value: 0x60
    steps:
      - AluSp | Add | CF1 | AluToSp
      - SP | AluM | AluToAddrL
      - AluSp | Add | CF1 | AluToSp
      - SP | AluM | AluToAddrH
      - CntLIn | CntHIn
      - CntEn
  - name: "SBC #$44"
    value: 0xe9
    steps:
      - AluM | AluA | Sub | CF | AluToA | NFEn | VFEn | ZFEn | CFEn | CntEn
  - name: "SBC $44"
    value: 0xe5
    prefix: ZP
    steps:
      - Addr | AluM | AluA | Sub | CF | AluToA | NFEn | VFEn | ZFEn | CFEn
  - name: "SBC $44,X"
    value: 0xf5
    prefix: ZPX
    steps:
      - Addr | AluM | AluA | Sub | CF | AluToA | NFEn | VFEn | ZFEn | CFEn
  - name: "SBC $4400"
    value: 0xed
    prefix: Abs
    steps:
      - Addr | AluM | AluA | Sub | CF | AluToA | NFEn | VFEn | ZFEn | CFEn
  - name: "SBC $4400,X"
    value: 0xfd
    prefix: AbsX
    steps:
      - Addr | AluM | AluA | Sub | CF | AluToA | NFEn | VFEn | ZFEn | CFEn
  - name: "SBC $4400,Y"
    value: 0xf9
    prefix: AbsY
    steps:
      - Addr | AluM | AluA | Sub | CF | AluToA | NFEn | VFEn | ZFEn | CFEn
  - name: "SBC ($44,X)"
    value: 0xe1
    prefix: IndX
    steps:
      - Addr | AluM | AluA | Sub | CF | AluToA | NFEn | VFEn | ZFEn | CFEn
  - name: "SBC ($44),Y"
    value: 0xf1
    prefix: IndY
    steps:
      - Addr | AluM | AluA | Sub | CF | AluToA | NFEn | VFEn | ZFEn | CFEn
  - name: "STA $44"
    value: 0x85
    prefix: ZP
    steps:
      - Addr | DataOutA
  - name: "STA $44,X"
    value: 0x95
    prefix: ZPX
    steps:
      - Addr | DataOutA
  - name: "STA $4400"
    value: 0x8D
    prefix: Abs
    steps:
      - Addr | DataOutA
  - name: "STA $4400,X"
    value: 0x9d
    prefix: AbsX
    steps:
      - Addr | DataOutA
  - name: "STA $4400,Y"
    value: 0x99
    prefix: AbsY
    steps:
      - Addr | DataOutA
  - name: "STA ($44,X)"
    value: 0x81
    prefix: IndX
    steps:
      - Addr | DataOutA
  - name: "STA ($44),Y"
    value: 0x91
    prefix: IndY
    steps:
      - Addr | DataOutA
  - name: "TXS"
    value: 0x9a
    steps:
      - SP | DataOutX
      - AluSp | Sub | CF1 | AluToSp
  - name: "TSX"
    value: 0xba
    steps:
      - AluSp | Add | CF1 | AluToSp
      - SP | AluM | AluToX
  - name: "PHA"
    value: 0x48
    steps:
      - SP | DataOutA
      - AluSp | Sub | CF1 | AluToSp
  - name: "PLA"
    value: 0x68
    steps:
      - AluSp | Add | CF1 | AluToSp
      - SP | AluM | AluToA
  - name: "PHP"
    value: 0x08
    steps:
      - SP | DataOutF
      - AluSp | Sub | CF1 | AluToSp
  - name: "PLP"
    value: 0x28
    steps:
      - AluSp | Add | CF1 | AluToSp
      - SP | AluM | AluToF
  - name: "STX $44"
    value: 0x86
    prefix: ZP
    steps:
      - Addr | DataOutX
  - name: "STX $44,Y"
    value: 0x96
    prefix: ZPY
    steps:
      - Addr | DataOutX
  - name: "STX $4400"
    value: 0x8e
    prefix: Abs
    steps:
      - Addr | DataOutX
  - name: "STY $44"
    value: 0x84
    prefix: ZP
    steps:
      - Addr | DataOutY
  - name: "STY $44,X"
    value: 0x94
    prefix: ZPX
    steps:
      - Addr | DataOutY
  - name: "STY $4400"
    value: 0x8c
    prefix: Abs
    steps:
      - Addr | DataOutY
  - name: "Reset"
    value: 0xFF
    type: full
    steps:
      - InstIn
      - CntLIn | CntEn | CntHIn | AluSp | Sub | CF1 | AluToSp
      - CntLIn | CntEn
      - CntLIn | CntEn
      - CntLIn | CntEn | AluM | AluToAddrH
      - AluM | AluToAddrL
      - CntLIn | CntHIn
